komppa/ATS/include/ZMPT101B.h

#ifndef ZMPT101B_h
#define ZMPT101B_h

#ifndef UNIT_TEST
#include <Arduino.h>

#include <stdint.h>

#define ADC_SCALE 1023.0
#define VREF 5.0
#define DEFAULT_FREQUENCY 50

class ZMPT101B {
public:
	ZMPT101B(uint8_t _pin);
	int calibrate();
	void setZeroPoint(int _zero);
	void setSensitivity(float sens);
	float getSensitivity(); 
	float getVoltageDC();
	float getVoltageAC(uint16_t frequency = 50);

private:
	int zero = 512;
	float sensitivity;
	uint8_t pin;
};

#endif

#endif	// UNIT_TEST
