komppa/ATS/src/ZMPT101B.cpp

#include "ZMPT101B.h"

#ifndef UNIT_TEST


ZMPT101B::ZMPT101B(uint8_t _pin) {
	pin = _pin;
	sensitivity = 0.019;
}

int ZMPT101B::calibrate() {
	uint16_t acc = 0;
	for (int i = 0; i < 10; i++) {
		acc += analogRead(pin);
	}
	zero = acc / 10;
	return zero;
}

void ZMPT101B::setZeroPoint(int _zero) {
	zero = _zero;
}

void ZMPT101B::setSensitivity(float sens) {
	sensitivity = sens;
}

float ZMPT101B::getSensitivity() {
	return this->sensitivity;
}

float ZMPT101B::getVoltageDC() {
	int16_t acc = 0;
	for (int i = 0; i < 10; i++) {
		acc += analogRead(pin) - zero;
	}
	float V = (float)acc / 10.0 / ADC_SCALE * VREF / sensitivity;
	return V;
}

float ZMPT101B::getVoltageAC(uint16_t frequency) {
	uint32_t period = 1000000 / frequency;
	uint32_t t_start = micros();

	uint32_t Vsum = 0, measurements_count = 0;
	int32_t Vnow;

	while (micros() - t_start < period) {
		Vnow = analogRead(pin) - zero;
		Vsum += Vnow*Vnow;
		measurements_count++;
	}

	float Vrms = sqrt(Vsum / measurements_count) / ADC_SCALE * VREF / sensitivity;
	return Vrms;
}

#endif // UNIT_TEST
